manuelkasper/kxusbc2/firmware/src/charger_sm.c

#include "charger_sm.h"
#include "bq.h"
#include "fsc_pd_ctl.h"
#include "platform.h"
#include "kx2.h"
#include "led.h"
#include "sysconfig.h"
#include "debug.h"
#include "rtc.h"
#include "fsc_pd/timer.h"
#include <avr/io.h>

static ChargerState current_state;
static ChargerState pre_fault_state;
static uint16_t otg_voltage;
static uint16_t otg_current;
static struct TimerObj state_timer;
static bool discharging_low_battery = false;

static void update_led_for_state(void);
static void check_fault_conditions(void);
static void set_state(ChargerState new_state);
static bool check_rig_inhibit(void);
static void update_charging_led(void);

/* State-specific functions (grouped by state) */
static void enter_disconnected(void);
static void exit_disconnected(void);
static uint16_t handle_disconnected(void);

static void enter_dc_charging(void);
static uint16_t handle_dc_charging(void);

static void enter_usb_negotiating(void);
static uint16_t handle_usb_negotiating(void);

static void enter_usb_type_c_charging(void);
static uint16_t handle_usb_type_c_charging(void);

static void enter_usb_pd_charging(void);
static uint16_t handle_usb_pd_charging(void);

static void enter_rig_on(void);
static uint16_t handle_rig_on(void);

static void enter_discharging(void);
static uint16_t handle_discharging(void);
static uint16_t handle_discharging_blocked(void);

static uint16_t handle_fault(void);

/* ===== Initialization ===== */

bool charger_sm_init(void) {
    current_state = CHARGER_DISCONNECTED;
    pre_fault_state = CHARGER_DISCONNECTED;
    otg_voltage = 0;
    otg_current = 0;
    discharging_low_battery = false;
    TimerDisable(&state_timer);
    return true;
}

/* ===== Event Handlers ===== */

void charger_sm_on_bq_interrupt(void) {
    // BQ interrupt will be detected by state machine checking hardware status
    // No action needed here - state machine queries BQ directly
    //debug_printf("SM: BQ interrupt received\n");
}

void charger_sm_on_pd_state_change(void) {
    // PD state will be detected by state machine checking connection state
    // No action needed here - state machine queries fsc_pd directly
    debug_printf("SM: PD state change: %d, %d\n", fsc_pd_get_connection_state(), fsc_pd_get_policy_state());
}

void charger_sm_on_pps_voltage_update(uint16_t mv) {
    // Skip if no change
    if (otg_voltage == mv) {
        return;
    }

    otg_voltage = mv;

    // When PPS voltage is set to non-zero, PD has negotiated OTG mode
    // Configure BQ and transition to DISCHARGING state
    if (otg_voltage > 0) {
        // Don't allow OTG if we've already hit the low battery limit
        // Must enter a charging state first to clear the flag
        if (discharging_low_battery) {
            debug_printf("SM: OTG mode rejected - must recharge first\n");
            set_state(CHARGER_DISCHARGING_BLOCKED);
            return;
        }

        // If there is an input voltage on VAC2 (DC jack), we cannot enter OTG mode.
        // The charger IC seems to have a restriction, and no matter what we do with
        // EN_ACDRV1/2 and DIS_ACDRV, OTG mode will not start as long as there is an
        // input voltage on VAC2. The datasheet is not clear on this point, but this
        // forum post by a TI employee seems to confirm it:
        // https://e2e.ti.com/support/power-management-group/power-management/f/power-management-forum/1546390/bq25792-otg-use-case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
        // However, if OTG is already active and the DC jack is then plugged in,
        // OTG will continue to function normally.
        if (bq_get_ac2_present()) {
            debug_printf("SM: Cannot enter OTG mode while DC jack is connected\n");
            return;
        }
        bq_disable_charging();
        bq_set_acdrv(true, false);
        if (otg_current == 0) {
            // No current limit set yet - use configured default
            otg_current = sysconfig->otgCurrentLimit;
            bq_set_otg_current_limit(otg_current + OTG_CURRENT_HEADROOM);
        }
        uint16_t otg_voltage_eff = otg_voltage;
        if (sysconfig->otgVoltageHeadroom <= OTG_VOLTAGE_HEADROOM_LIMIT) {
            // Limit headroom for safety
            otg_voltage_eff += sysconfig->otgVoltageHeadroom;
        }
        bq_enable_otg(otg_voltage_eff);
        set_state(CHARGER_DISCHARGING);
    } else {
        // OTG mode ended
        bq_disable_otg();
        if (current_state == CHARGER_DISCHARGING) {
            set_state(CHARGER_DISCONNECTED);
        }
    }
}

void charger_sm_on_pps_current_update(uint16_t ma) {
    if (ma > sysconfig->otgCurrentLimit) {
        ma = sysconfig->otgCurrentLimit;
    }

    // Skip if no change
    if (otg_current == ma) {
        return;
    }

    otg_current = ma;

    // Configure BQ with the new current limit. Add a generous headroom to ensure we don't run into
    // IOTG regulation if the current drawn by the load slightly exceeds the advertised current
    // (e.g. due to measurement inaccuracies or load transients).
    // Otherwise, the IOTG limit will cause VOTG to drop (CC mode), which could lead to a PD reset.
    // Despite the name of this function and the related code in fsc_pd, we don't advertise PPS mode,
    // and thus don't need to guarantee accurate current limits.
    bq_set_otg_current_limit(otg_current + OTG_CURRENT_HEADROOM);
}

/* ===== State Machine Core ===== */

/**
 * @brief Check if rig inhibit is active and transition to RIG_ON if needed
 * @return true if inhibited (transitioned to RIG_ON), false otherwise
 */
static bool check_rig_inhibit(void) {
    if (kx2_is_on() && !sysconfig->chargeWhenRigIsOn) {
        set_state(CHARGER_RIG_ON);
        return true;
    }
    return false;
}

uint16_t charger_sm_run(void) {
    //debug_printf("SM: Current state: %d\n", current_state);

    // Check for faults every cycle
    check_fault_conditions();

    // Dispatch to state-specific handler
    uint16_t timeout = 0;
    switch (current_state) {
        case CHARGER_DISCONNECTED:
            timeout = handle_disconnected();
            break;
        case CHARGER_DC_CHARGING:
            timeout = handle_dc_charging();
            break;
        case CHARGER_USB_NEGOTIATING:
            timeout = handle_usb_negotiating();
            break;
        case CHARGER_USB_TYPE_C_CHARGING:
            timeout = handle_usb_type_c_charging();
            break;
        case CHARGER_USB_PD_CHARGING:
            timeout = handle_usb_pd_charging();
            break;
        case CHARGER_RIG_ON:
            timeout = handle_rig_on();
            break;
        case CHARGER_DISCHARGING:
            timeout = handle_discharging();
            break;
        case CHARGER_DISCHARGING_BLOCKED:
            timeout = handle_discharging_blocked();
            break;
        case CHARGER_FAULT:
            timeout = handle_fault();
            break;
        default:
            // Reserved/unused states - fall back to disconnected
            set_state(CHARGER_DISCONNECTED);
            break;
    }

    update_led_for_state();

    return timeout;
}

/* ================================================================================
 * CHARGER_DISCONNECTED - No input present
 * ================================================================================ */

static void enter_disconnected(void) {
    bq_disable_charging();
    bq_disable_otg();
    bq_disable_adc();
    otg_voltage = 0;
    otg_current = 0;
    led_shutdown();
}

static void exit_disconnected(void) {
    led_wakeup();
}

static uint16_t handle_disconnected(void) {
    // Check if any input available
    if (bq_get_ac2_present()) {
        set_state(CHARGER_DC_CHARGING);
    } else if (bq_get_ac1_present()) {
        if (fsc_pd_get_connection_state() == AttachedSink) {
            set_state(CHARGER_USB_NEGOTIATING);
        }
    }
    return 0;
}

/* ================================================================================
 * CHARGER_DC_CHARGING - DC jack connected
 * ================================================================================ */

static void enter_dc_charging(void) {
    discharging_low_battery = false;  // Clear low battery flag when entering charging
    bq_set_acdrv(false, true);
    bq_set_input_current_limit(sysconfig->dcInputCurrentLimit);
    bq_enable_adc();
    
    if (!kx2_is_on() || sysconfig->chargeWhenRigIsOn) {
        bq_enable_charging();
    }
}

static uint16_t handle_dc_charging(void) {
    // Check if KX2 turned on
    if (check_rig_inhibit()) {
        return 0;
    }
    
    // DC jack charging
    if (!bq_get_ac2_present()) {
        // DC removed, check USB
        if (bq_get_ac1_present()) {
            ConnectionState conn = fsc_pd_get_connection_state();
            if (conn == AttachedSink) {
                set_state(CHARGER_USB_NEGOTIATING);
            }
        } else {
            set_state(CHARGER_DISCONNECTED);
        }
    }
    return 0;
}

/* ================================================================================
 * CHARGER_USB_NEGOTIATING - USB attached, waiting for PD negotiation
 * ================================================================================ */

static void enter_usb_negotiating(void) {
    // USB attached, waiting for PD negotiation
    bq_set_acdrv(true, false);
    // Set default current while waiting for negotiation
    bq_set_input_current_limit(fsc_pd_get_advertised_current());

    // Don't enable charging yet - wait for negotiation or timeout
    TimerStart(&state_timer, PD_NEGOTIATION_TIMEOUT); // 3s negotiation timeout
}

static uint16_t handle_usb_negotiating(void) {
    // Check if KX2 turned on
    if (check_rig_inhibit()) {
        return 0;
    }
    
    // Check negotiation timeout
    if (TimerExpired(&state_timer)) {
        // Negotiation timeout - fall back to Type-C
        set_state(CHARGER_USB_TYPE_C_CHARGING);
    } else if (fsc_pd_policy_has_contract()) {
        // Contract established
        set_state(CHARGER_USB_PD_CHARGING);
    } else if (!bq_get_ac1_present()) {
        // USB disconnected
        set_state(CHARGER_DISCONNECTED);
    }
    return TimerRemaining(&state_timer);
}

/* ================================================================================
 * CHARGER_USB_TYPE_C_CHARGING - USB Type-C without PD
 * ================================================================================ */

static void enter_usb_type_c_charging(void) {
    discharging_low_battery = false;  // Clear low battery flag when entering charging
    // Type-C negotiated without PD (5 V / 0.5..3 A)
    uint16_t adv_current = fsc_pd_get_advertised_current();

    if (adv_current == 500) {
        // No PD contract and default current. May not be a Type-C connector. Leave it up to BC1.2 detection,
        // which automatically sets the current limit after D+/D- detection.
        bq_enable_bc12_detection();
    } else {
        // Type C negotiated - disable BC1.2 detection and use negotiated current
        bq_disable_bc12_detection();
        bq_set_input_current_limit(adv_current);
    }
    
    bq_enable_adc();
    bq_enable_charging();
}

static uint16_t handle_usb_type_c_charging(void) {
    // Check if KX2 turned on
    if (check_rig_inhibit()) {
        return 0;
    }
    
    // Monitor advertised current changes
    uint16_t adv_current = fsc_pd_get_advertised_current();
    if (adv_current != 500) {
        // Type-C current changed - update BQ
        bq_set_input_current_limit(adv_current);
    }
    
    if (fsc_pd_get_connection_state() != AttachedSink) {
        set_state(CHARGER_DISCONNECTED);
    } else if (fsc_pd_policy_has_contract()) {
        set_state(CHARGER_USB_PD_CHARGING);
    }
    return 0;
}

/* ================================================================================
 * CHARGER_USB_PD_CHARGING - USB with PD negotiated contract
 * ================================================================================ */

static void enter_usb_pd_charging(void) {
    discharging_low_battery = false;  // Clear low battery flag when entering charging
    // PD contract established
    uint16_t adv_current = fsc_pd_get_advertised_current();
    
    bq_disable_bc12_detection();
    bq_set_input_current_limit(adv_current);
    bq_enable_adc();
    bq_enable_charging();
}

static uint16_t handle_usb_pd_charging(void) {
    // Check if KX2 turned on
    if (check_rig_inhibit()) {
        return 0;
    }
    
    // Monitor advertised current changes
    uint16_t adv_current = fsc_pd_get_advertised_current();
    bq_set_input_current_limit(adv_current);
    
    if (fsc_pd_get_connection_state() != AttachedSink) {
        set_state(CHARGER_DISCONNECTED);
    } else if (!fsc_pd_policy_has_contract()) {
        set_state(CHARGER_USB_TYPE_C_CHARGING);
    }
    return 0;
}

/* ================================================================================
 * CHARGER_RIG_ON - Rig powered on, charging inhibited
 * ================================================================================ */

static void enter_rig_on(void) {
    bq_disable_charging();
}

static uint16_t handle_rig_on(void) {
    // Rig powered, charging inhibited
    if (!kx2_is_on()) {
        // Rig powered down - return to disconnected for clean restart
        set_state(CHARGER_DISCONNECTED);
    } else if (!bq_get_ac1_present() && !bq_get_ac2_present()) {
        // Input power disappeared while rig is on
        set_state(CHARGER_DISCONNECTED);
    }
    return 0;
}

/* ================================================================================
 * CHARGER_DISCHARGING - OTG mode (providing power)
 * ================================================================================ */

static void enter_discharging(void) {
    bq_enable_adc();
}

static uint16_t handle_discharging(void) {
    // OTG mode (providing power)
    ConnectionState conn = fsc_pd_get_connection_state();
    if (conn != AttachedSource) {
        // Role swap or disconnected
        bq_disable_otg();
        set_state(CHARGER_DISCONNECTED);
        return 0;
    }

    // Monitor battery voltage during discharging
    uint16_t vbat = bq_measure_vbat();
    if (vbat > 0 && vbat < sysconfig->dischargingVoltageLimit) {
        if (!discharging_low_battery) {
            discharging_low_battery = true;
            debug_printf("SM: Battery voltage too low for discharging: %u mV < %u mV\n", 
                        vbat, sysconfig->dischargingVoltageLimit);
            bq_disable_otg();
            set_state(CHARGER_DISCHARGING_BLOCKED);
        }
    }
    
    return 0;
}

/* ================================================================================
 * CHARGER_DISCHARGING_BLOCKED - OTG mode blocked due to low battery
 * ================================================================================ */

static uint16_t handle_discharging_blocked(void) {
    // OTG mode was requested but blocked due to low battery
    
    if (fsc_pd_get_connection_state() != AttachedSource) {
        // Role swap or disconnected
        set_state(CHARGER_DISCONNECTED);
        return 0;
    }
    
    return 0;
}

/* ================================================================================
 * CHARGER_FAULT - Fault condition detected
 * ================================================================================ */

static uint16_t handle_fault(void) {
    // Stay in fault state until input is disconnected
    if (!bq_get_ac1_present() && !bq_get_ac2_present()) {
        set_state(CHARGER_DISCONNECTED);
    }
    return 0;
}

/* ===== State transition handling ===== */

static void set_state(ChargerState new_state) {
    if (new_state == current_state) {
        return;
    }

    ChargerState previous_state = current_state;
    current_state = new_state;

    debug_printf("SM: State transition %d -> %d\n", previous_state, new_state);

    // Disable any active timers when changing state
    TimerDisable(&state_timer);

    // Call exit handler for previous state
    switch (previous_state) {
        case CHARGER_DISCONNECTED:
            exit_disconnected();
            break;
        default:
            break;
    }

    // Call entry handler for new state
    switch (new_state) {
        case CHARGER_DISCONNECTED:
            enter_disconnected();
            break;
        case CHARGER_DC_CHARGING:
            enter_dc_charging();
            break;
        case CHARGER_USB_NEGOTIATING:
            enter_usb_negotiating();
            break;
        case CHARGER_USB_TYPE_C_CHARGING:
            enter_usb_type_c_charging();
            break;
        case CHARGER_USB_PD_CHARGING:
            enter_usb_pd_charging();
            break;
        case CHARGER_RIG_ON:
            enter_rig_on();
            break;
        case CHARGER_DISCHARGING:
            enter_discharging();
            break;
        default:
            break;
    }

    update_led_for_state();
}

static void update_led_for_state(void) {
    switch (current_state) {
        case CHARGER_FAULT:
            led_set_blinking(true, false, false, 255, 2, 2, 15, 0);  // Red blinking at 5 Hz
            break;

        case CHARGER_USB_NEGOTIATING:
            led_set_blinking(false, true, false, 255, 2, 2, 15, 0);  // Green blinking at 5 Hz
            break;

        case CHARGER_USB_TYPE_C_CHARGING:
        case CHARGER_USB_PD_CHARGING:
        case CHARGER_DC_CHARGING:
            update_charging_led();
            break;

        case CHARGER_RIG_ON:
            led_set_color(true, false, true, 255);  // Magenta - Rig powered
            break;

        case CHARGER_DISCHARGING:
            update_charging_led();
            break;

        case CHARGER_DISCHARGING_BLOCKED:
            // Show red blinking to indicate battery too low for OTG
            led_set_blinking(true, false, false, 255, 5, 5, 15, 0);  // Red blinking at 2 Hz
            break;
        
        default:
            led_off();
            break;
    }
}

static void update_charging_led(void) {
    // Check temperature and charge status
    TemperatureStatus temp_status = bq_get_temperature_status();
    ChargeStatus charge_status = bq_get_charge_status();

    if (temp_status & (TEMP_HOT | TEMP_COLD)) {
        // Hot or cold - (dis)charging is suspended
        led_set_color(true, false, false, 255); // Red
    } else {
        // Color depends on temperature - green (or blue) for normal, yellow (or cyan) for warm/cool
        bool warm_cool = (temp_status & (TEMP_WARM | TEMP_COOL)) ? true : false;
        int16_t battery_current = bq_measure_ibat();

        if (current_state == CHARGER_DISCHARGING) {
            battery_current = -battery_current;
        }

        // LED "breathing" speed depends on (dis)charging current.
        // Hysteresis: downward transitions (slower speed) require 100 mA below the threshold
        // to avoid rapid toggling when current fluctuates near a boundary.
        static uint8_t breathing_speed = 7;
        int16_t thresh_fast   = (breathing_speed > 1) ? 2000 : 1900;
        int16_t thresh_medium = (breathing_speed > 3) ? 1000 : 900;
        int16_t thresh_slow   = (breathing_speed > 5) ? 500  : 400;

        if (battery_current >= thresh_fast) {
            // Fast charging
            breathing_speed = 1;
        } else if (battery_current >= thresh_medium) {
            // Medium charging
            breathing_speed = 3;
        } else if (battery_current >= thresh_slow) {
            // Slow charging
            breathing_speed = 5;
        } else {
            // Very slow charging
            breathing_speed = 7;
        }

        if (current_state == CHARGER_DISCHARGING) {
            // OTG mode - blue/cyan breathing
            led_set_breathing(false, warm_cool, true, 255, breathing_speed);
        } else {
            // Have we finished charging?
            if (charge_status == CHARGE_DONE) {
                led_set_color(false, true, false, 255); // Green
            } else {
                // Charging - green/yellow breathing
                led_set_breathing(warm_cool, true, false, 255, breathing_speed);
            }
        }
    }
}

static void check_fault_conditions(void) {
    // Detect new faults
    if (bq_get_fault_status() != 0) {
        if (current_state != CHARGER_FAULT) {
            pre_fault_state = current_state;
            debug_printf("SM: Fault detected: %x\n", bq_get_fault_status());
            set_state(CHARGER_FAULT);
        }
    } else {
        // No fault
        if (current_state == CHARGER_FAULT) {
            debug_printf("SM: Fault cleared, returning to state %d\n", pre_fault_state);
            set_state(pre_fault_state);
        }
    }
}

/* ===== Getters ===== */

ChargerState charger_sm_get_state(void) {
    return current_state;
}
